J-Rios/SWNUI/Project/Software/SWNUI/main_program/main_program.ino

#include "SWNUI.h"

/***********************************************************************************/

SWNUI swnui;

/***********************************************************************************/

void setup()
{
    swnui.init();
}

void loop()
{
    swnui.update();
}

/***********************************************************************************/
